bwburnsides/BW8cpu/graphics/gouldian.png

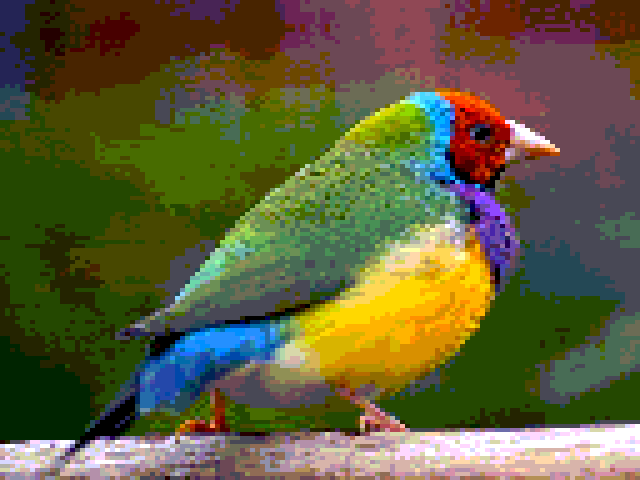
graphics/gouldian.png
