bwburnsides/BW8cpu/graphics/roof_korean.png

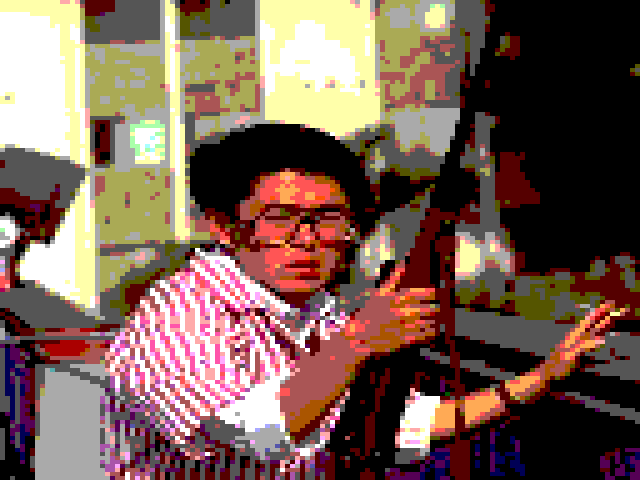
graphics/roof_korean.png
