bwburnsides/BW8cpu/graphics/sn15.png

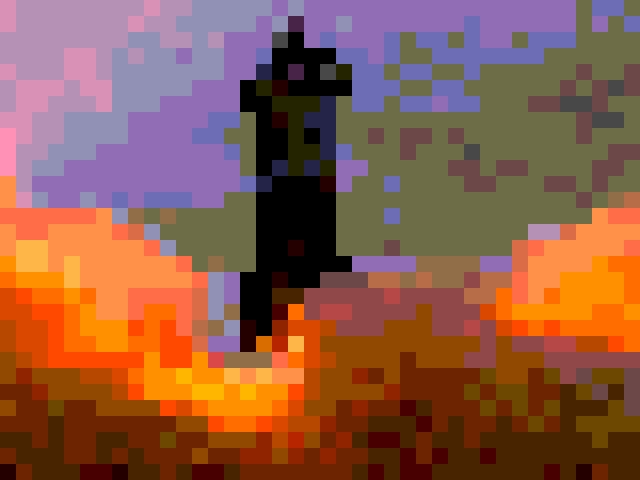
graphics/sn15.png
