bwburnsides/BW8cpu/assembler/foo.asm

#include "bw8cpu.asm"

#bankdef program_memory {
    #addr 0x0000
    #size 0xFFFF
    #outp 0
    #fill
}

load a, #0xff
load a, #0xff
load a, #0xff
load a, #0xff
load a, #0xff
load a, #0xff
load a, #0xff
load a, #0xff
load a, #0xff
load a, #0xff
load a, #0xff
load a, #0xff
load a, #0xff
load a, #0xff
load a, #0xff
load a, #0xff
load a, #0xff
load a, #0xff
load a, #0xff
load a, #0xff
load a, #0xff
load a, #0xff
load a, #0xff
load a, #0xff
load a, #0xff
load a, #0xff
load a, #0xff
load a, #0xff
load a, #0xff
load a, #0xff
load a, #0xff
load a, #0xff
load a, #0xff
load a, #0xff
load a, #0xff
load a, #0xff
load a, #0xff
load a, #0xff
load a, #0xff
load a, #0xff
load a, #0xff
load a, #0xff
load a, #0xff
load a, #0xff
load a, #0xff
load a, #0xff
load a, #0xff
load a, #0xff
load a, #0xff
load a, #0xff
load a, #0xff
load a, #0xff
load a, #0xff
load a, #0xff
load a, #0xff
load a, #0xff
load a, #0xff
load a, #0xff
load a, #0xff
load a, #0xff
load a, #0xff
load a, #0xff
load a, #0xff
load a, #0xff
load a, #0xff
load a, #0xff
load a, #0xff
load a, #0xff
load a, #0xff
load a, #0xff
load a, #0xff
load a, #0xff
load a, #0xff
load a, #0xff
load a, #0xff
load a, #0xff
load a, #0xff
load a, #0xff
load a, #0xff
load a, #0xff
load a, #0xff
load a, #0xff
load a, #0xff
load a, #0xff
load a, #0xff
load a, #0xff
load a, #0xff
load a, #0xff
load a, #0xff
load a, #0xff
load a, #0xff
load a, #0xff
load a, #0xff
load a, #0xff
load a, #0xff
load a, #0xff
load a, #0xff
load a, #0xff
load a, #0xff
load a, #0xff
load a, #0xff
load a, #0xff
load a, #0xff
load a, #0xff
load a, #0xff
